uggoth/EastDevonPirates2024/STL/ZyderBot 8 Front Window B.stl

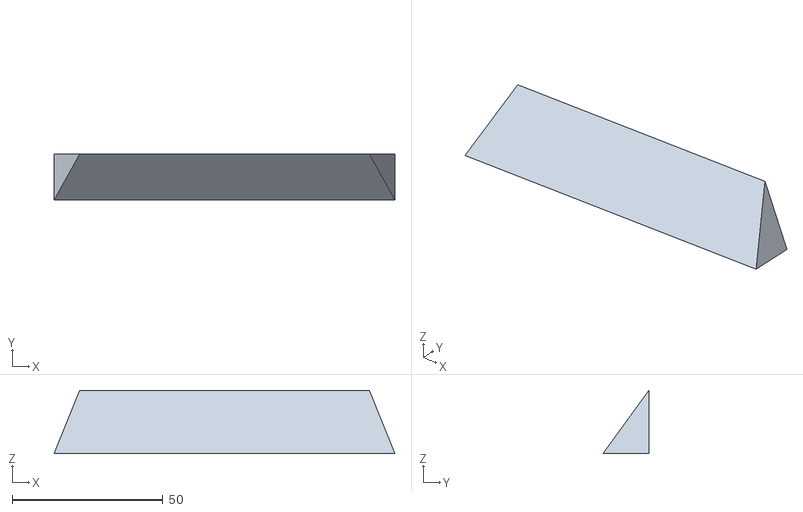
[picture p17: CAD file, 2023-10-29]
STL/ZyderBot 8 Front Window B.stl
113.0 x 15.3 x 21.0
