uggoth/EastDevonPirates2024/STL/ZyderBot 8 Chassis RTD.stl

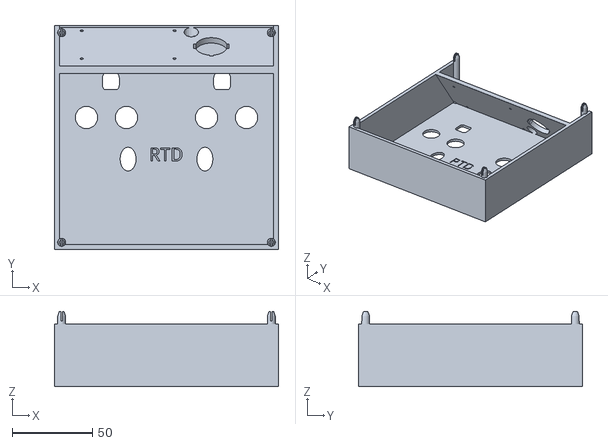
[picture p18: CAD file, 2023-10-29]
STL/ZyderBot 8 Chassis RTD.stl
140.0 x 140.0 x 47.0
