uggoth/EastDevonPirates2024/PicoCode/main_a_s_a_d_constants.py

module_name = 'main_a_s_a_d_constants.py'
print (module_name, 'starting')

PICO_NAME = 'PICOA'
BLUE_BUTTON_PIN_NO = 5
DIP_1_PIN_NO = 13
DIP_5_PIN_NO = 17
DIP_6_PIN_NO = 16
UART_TX_PIN_NO = 0
UART_RX_PIN_NO = 1
UART_NO = 0
UART_BAUD_RATE = 100000
LF_SPEED_PIN_NO = 2
LF_PULSE_PIN_NO = 3
LF_DIRECTION_PIN_NO = 4
RF_SPEED_PIN_NO = 6
RF_PULSE_PIN_NO = 7
RF_DIRECTION_PIN_NO = 8
LB_SPEED_PIN_NO = 10
LB_PULSE_PIN_NO = 11
LB_DIRECTION_PIN_NO = 12
RB_SPEED_PIN_NO = 21
RB_PULSE_PIN_NO = 20
RB_DIRECTION_PIN_NO = 19
HANDSHAKE_PIN_NO = 22
