uggoth/EastDevonPirates2024/PiCode/ColObjects_Pi_V15.py

module_name = 'ColObjects_v14.py'
module_created_at = '202305011105'

import math
import time

class ColError(Exception):
    def __init__(self, message):
        super().__init__(message)

class ColObj():
    
    allocated = {}
    free_code = 'FREE'
    
    def str_allocated():
        out_string = ('{:18}'.format('NAME') +
                        '{:18}'.format('OBJECT') + '\n')
        for name in sorted(ColObj.allocated):
            if ColObj.allocated[name] != ColObj.free_code:
                obj = ColObj.allocated[name]
                out_string += ('{:18}'.format(obj.name)  +
                                str(obj) + '\n')
        return out_string
    
    def __init__(self, name, description=''):
        self.name = name
        if name in ColObj.allocated:
            if ColObj.allocated[self.name] != ColObj.free_code:
                raise ColError(name + ' already allocated')
        ColObj.allocated[self.name] = self
        self.description = description
        
    def __str__(self):
        return self.name
    
    def close(self):
        ColObj.allocated[self.name] = ColObj.free_code

class Servo(ColObj):
    def __init__(self, name, description='Generic Servo'):
        super().__init__(name, description)
    def move_to(self, in_pos, speed):
        pos = int(in_pos)
        if pos < -100:
            raise ColError('pos must be between -100 and +100')
        if pos > 100:
            raise ColError('pos must be between -100 and +100')
        if speed < 1:
            raise ColError('speed must be between 1 and 100')
        if speed > 100:
            raise ColError('speed must be between 1 and 100')
    def close(self):
        super().close()

class Switch(ColObj):
    def __init__(self, name):
        super().__init__(name)
    def get(self):
        print ('MUST OVERRIDE')
    def close(self):
        super().close()

class Interpolator(ColObj):
    def __init__(self, name, keys, values): # arrays of matching pairs
                                            # keys ascending integers
                                            # values any floats
        super().__init__(name)
        self.keys = keys
        self.values = values
    def interpolate(self, in_key):  #  input is integer
        if in_key is None:
            return None
        below_ok = False
        above_ok = False
        for i in range(len(self.keys)):
            if in_key == self.keys[i]:
                return self.values[i]
            if in_key > self.keys[i]:
                below_key = self.keys[i]
                below_value = self.values[i]
                below_ok = True
            if in_key < self.keys[i]:
                above_key = self.keys[i]
                above_value = self.values[i]
                above_ok = True
                break
        if above_ok and below_ok:
            out_value = below_value + (((in_key - below_key) / (above_key - below_key)) * (above_value - below_value))
            return out_value
        else:
            return None


class Motor(ColObj):
    def __init__(self, name):
        super().__init__(name)
    def clk(self, speed):
        raise ColError('**** Must be overriden')
    def anti(self, speed):
        raise ColError('**** Must be overriden')
    def stop(self):
        raise ColError('**** Must be overriden')
    def close(self):
        super().close()

class Side(ColObj):
    def __init__(self, name, which_side, my_motors):
        super().__init__(name)
        self.which_side = which_side
        self.my_motors = my_motors
    def __str__(self):
        outstring = ''
        outstring += self.name + '  '
        for motor in self.my_motors:
            outstring += motor.name + '  '
    def fwd(self, speed):
        for motor in self.my_motors:
            if self.which_side == 'L':
                motor.anti(speed)
            else:
                motor.clk(speed)
    def rev(self, speed):
        for motor in self.my_motors:
            if self.which_side == 'L':
                motor.clk(speed)
            else:
                motor.anti(speed)
    def drive(self, speed):
        if speed < 0:
            self.rev(-speed)
        else:
            self.fwd(speed)
    def stop(self):
        for motor in self.my_motors:
            motor.stop()
    def close(self):
        for motor in self.my_motors:
            motor.close()
        super().close()

class DriveTrain(ColObj):
    def __init__(self, name, left_side, right_side):
        super().__init__(name)
        self.left_side = left_side
        self.right_side = right_side
        self.millimetre_factor = 30
        self.degree_factor = 30
        self.speed_exponent = 0.5          
        keys = [-101, -50, -2, 2, 50, 101]
        values = [1.0, 1.0, 1.0, 1.0, 0.0, -1.0]
        self.left_side_interpolator = Interpolator(name+'_remls',keys, values)
        values = [-1.0, 0.0, 1.0, 1.0, 1.0, 1.0]
        self.right_side_interpolator = Interpolator(name+'_remrs',keys, values)
    def calculate_speeds_car(self, throttle_value, steering_value):
        if ((throttle_value is None) or (steering_value is None)):
            return 0,0
        left_factor = self.left_side_interpolator.interpolate(steering_value)
        right_factor = self.right_side_interpolator.interpolate(steering_value)
        left_speed = int(throttle_value * left_factor)
        right_speed = int(throttle_value * right_factor)
        return left_speed, right_speed
    def drive(self, throttle_value, steering_value):
        left_speed, right_speed = self.calculate_speeds_car(throttle_value, steering_value)
        self.left_side.drive(left_speed)
        self.right_side.drive(right_speed)
    def fwd(self, speed=50, millimetres=50):
        self.left_side.fwd(speed)
        self.right_side.fwd(speed)
        if millimetres > 0:
            ms = self.convert_millimetres_to_milliseconds(millimetres, speed)
            time.sleep_ms(ms)
            self.stop()
            return ms
        return 0
    def rev(self, speed=50, millimetres=50):
        self.left_side.rev(speed)
        self.right_side.rev(speed)
        if millimetres > 0:
            ms = self.convert_millimetres_to_milliseconds(millimetres, speed)
            time.sleep_ms(ms)
            self.stop()
            return ms
        return 0
    def spl(self, speed=90, degrees=90):
        self.left_side.rev(speed)
        self.right_side.fwd(speed)
        if degrees > 0:
            ms = self.convert_degrees_to_milliseconds(degrees, speed)
            time.sleep_ms(ms)
            self.stop()
            return ms
        return 0
    def spr(self, speed=90, degrees=90):
        self.left_side.fwd(speed)
        self.right_side.rev(speed)
        if degrees > 0:
            ms = self.convert_degrees_to_milliseconds(degrees, speed)
            time.sleep_ms(ms)
            self.stop()
            return ms
        return 0
    def stop(self):
        self.left_side.stop()
        self.right_side.stop()
    def convert_millimetres_to_milliseconds(self, millimetres, speed):
        milliseconds = int (float(millimetres * self.millimetre_factor) / math.pow(speed, self.speed_exponent))
        return milliseconds
    def convert_degrees_to_milliseconds(self, millimetres, speed):
        degrees = int (float(millimetres * self.degree_factor) / math.pow(speed, self.speed_exponent))
        return degrees

class DriveTrainWithHeadlights(DriveTrain):
    def __init__(self, name, left_side, right_side, left_headlight, right_headlight):
        super().__init__(name, left_side, right_side)
        self.left_headlight = left_headlight
        self.right_headlight = right_headlight
    def fwd(self, speed=50, millimetres=50):
        self.left_headlight.on()
        self.right_headlight.on()
        super().fwd(speed, millimetres)
    def rev(self, speed=50, millimetres=50):
        self.left_headlight.red()
        self.right_headlight.red()
        super().rev(speed, millimetres)
    def spl(self, speed=90, degrees=90):
        self.left_headlight.purple()
        self.right_headlight.off()
        super().spl(speed, degrees)
    def spr(self, speed=90, degrees=90):
        self.left_headlight.off()
        self.right_headlight.purple()
        super().spr(speed, degrees)
    def stop(self):
        self.left_headlight.off()
        self.right_headlight.off()
        super().stop()

class DriveTrainPlus(DriveTrainWithHeadlights):
    def __init__(self, name, left_side, right_side, left_headlight, right_headlight,
                 front_left_ir, front_right_ir, rear_left_ir, rear_right_ir):
        super().__init__(name, left_side, right_side, left_headlight, right_headlight)
        self.front_left_ir = front_left_ir
        self.front_right_ir = front_right_ir
        self.rear_left_ir = rear_left_ir
        self.rear_right_ir = rear_right_ir
    def drive_for(self, throttle_value, steering_value, milliseconds):
        self.drive(throttle_value, steering_value)
        time.sleep_ms(milliseconds)
        self.stop()
    def drive_while(self, throttle_value, steering_value, obj_list):
        self.drive(throttle_value, steering_value)
        loop_count = 0
        loop_duration = 5
        all_ok = True
        while all_ok:
            for i in range(len(obj_list)):
                obj = obj_list[i][0]
                state = obj_list[i][1]
                current = obj.get()
                if current != state:
                    all_ok = False
            time.sleep_ms(loop_duration)
            loop_count += 1
            current = obj.get()
        self.stop()
        return loop_count * loop_duration

class DriveCalc():
    
    def __init__(self, min_throttle, max_throttle, min_steering, max_steering):
        self.min_throttle = min_throttle
        self.max_throttle = max_throttle
        self.min_steering = min_steering
        self.max_steering = max_steering

    def constrain(self, n, lowest, highest):
        if n > highest:
            a = highest
        elif n < lowest:
            a = lowest
        else:
            a = n
        return a
        
    def get_drive_parms(self, mode, throttle, steering):
        #  returns left side speed, right side speed
        if mode == 'TANK':
            left = self.constrain (throttle, self.min_throttle, self.max_throttle)
            right = self.constrain (steering, self.min_steering, self.max_steering)
            return int(left), int(right)
        if mode == 'MIX':
            left = self.constrain (throttle + steering, self.min_throttle, self.max_throttle)
            right = self.constrain (throttle - steering, self.min_throttle, self.max_throttle)
            return int(left), int(right)


class RGBLED(ColObj):
    def __init__(self, name, red_led, green_led, blue_led):
        response = super().__init__(name)
        self.red_led = red_led
        self.green_led = green_led
        self.blue_led = blue_led
        
    def on(self):
        self.red_led.on()
        self.green_led.on()
        self.blue_led.on()

    def red(self):
        self.red_led.on()
        self.green_led.off()
        self.blue_led.off()

    def green(self):
        self.red_led.off()
        self.green_led.on()
        self.red_led.off()

    def blue(self):
        self.red_led.off()
        self.green_led.off()
        self.blue_led.on()

    def purple(self):
        self.red_led.on()
        self.green_led.off()
        self.blue_led.on()

    def orange(self):
        self.red_led.on()
        self.green_led.on()
        self.blue_led.off()

    def off(self):
        self.red_led.off()
        self.green_led.off()
        self.blue_led.off()
        
    def close(self):
        self.off()
        self.red_led.close()
        self.green_led.close()
        self.blue_led.close()

if __name__ == "__main__":
    print (module_name,'was created at',module_created_at)
    #d1 = PIO('Fred',1)
    #d2 = PIO('Bill',1)
    #d3 = PIO('George',0)
    #print (PIO.str_allocated())
    #PIO.deallocate(4)
    #print (PIO.str_allocated())
