uggoth/EastDevonPirates2024/PiCode/posing_setup_small_v25.py

module_name = 'posing_setup_small_v25.py'

print (module_name, 'starting')

import tkinter as tk
import AX12_Servo_V01 as AX12_Servo
Connection = AX12_Servo.Connection

class ServoSlider:
    def __init__(self, master, x_origin, y_origin, servo):
        self.master = master
        self.servo = servo
        self.my_name = self.servo.name
        self.my_min = -100
        self.my_max = 100
        self.my_var = tk.IntVar()
        self.my_slider = tk.Scale(master, command=self.slider_moved,
                                    from_=self.my_min,
                                    to=self.my_max,
                                    length=650, sliderlength=20, variable=self.my_var,
                                    orient=tk.HORIZONTAL, label=self.servo.name)
        pos = servo.get_position()
        self.my_slider.set(pos)
        self.my_slider.place(x=x_origin,y=y_origin)
        self.previous = {}
        self.previous['POS'] = 0
        self.ok_colour = '#EEEEEE'
        self.bad_colour = '#FF7777'
        self.clock_label = tk.Label(master, text='<<<  ' + self.servo.clockwise_label, bg=self.ok_colour)
        self.clock_label.place(x=x_origin + 150, y=y_origin)
        self.pos_label = tk.Label(master, text='POS: '+str(self.previous['POS']), bg=self.ok_colour)
        self.pos_label.place(x=x_origin + 300, y=y_origin)
        self.anti_label = tk.Label(master, text=self.servo.anticlockwise_label + '  >>>', bg=self.ok_colour)
        self.anti_label.place(x=x_origin + 450, y=y_origin)
        self.passive = False

    def get_pos_text(self, position):
        return 'POS: ' + str(position)
        
    def move_to_position(self, position):
        self.passive = False
        self.my_slider.set(position)

    def slider_moved(self, value):
        if not self.passive:
            self.servo.move_to(value)

    def changed(self):
        pos = self.servo.get_position()
        if pos != self.previous['POS']:
            self.pos_label.configure(text=get_pos_text(pos))
            self.previous['POS'] = pos
        return pos

    def set_slider_to_position(self, position):
        self.passive = True
        self.my_slider.set(position)
        self.passive = False

    def set_slider_to_current(self):
        self.passive = True
        position = self.servo.get_position()
        self.my_slider.set(position)
        self.passive = False

    def set_label_to_position(self, position):
        self.pos_label.configure(text=self.get_pos_text(position))

    def set_label_to_current(self):
        position = self.servo.get_position()
        self.pos_label.configure(text=self.get_pos_text(position))

class Calibrator:

    def __init__(self, master, width, height, servo_list):
        self.master = master
        self.frame_width = width
        self.frame_height = height
        self.servo_list = servo_list
        self.frame = tk.Frame(master, width=self.frame_width, height=self.frame_height)
        self.frame.owning_object = self
        self.frame.pack()
        x_left = 10
        y_top = 10
        x_interval = 50
        y_interval = 70
        self.speed = 50
        self.speed_factor = 2
        self.sliders = {}
        x_now = x_left
        y_now = y_top
        for servo in self.servo_list:
            self.sliders[servo.name] = ServoSlider(self.frame, x_now, y_now, servo)
            y_now += y_interval

#       SPEED

        x_now = x_left
        y_now += y_interval
        self.speed_var = tk.IntVar()
        self.speed_slider = tk.Scale(self.frame, command=self.speed_change,
                                        from_=0,
                                        to=100,
                                        length=350, sliderlength=20, variable=self.speed_var,
                                        orient=tk.HORIZONTAL, label='SPEED')
        self.speed_slider.set(50)
        self.speed_slider.place(x=x_now,y=y_now)
        
#       INDICATORS
#        x_now += (x_interval * 8)
#        self.volts = voltage_monitor.VoltageMonitor(self.frame, x_now, y_now, 'WRIS')
#        x_now += (x_interval * 3)
#        self.down_ir = ir_monitor.IRMonitor(self.frame, x_now, y_now,'DOWN_IR')

    def get_speed(self):
        return int(self.speed_var.get()) * self.speed_factor

    def speed_change(self, slider_position):
        self.speed = self.get_speed()


def my_loop(my_calibrator):
    for servo in my_calibrator.servo_list:
        my_calibrator.sliders[servo.name].set_label_to_current()
#    my_calibrator.down_ir.set_text()
#    my_calibrator.volts.set_text()
    root.after(10, my_loop, my_calibrator)   # milliseconds

ax12_connection = Connection(port='/dev/serial/by-id/usb-FTDI_USB__-__Serial_Converter_FT4TCSBK-if00-port0', baudrate=1000000)
base_servo = AX12_Servo.AX12_Servo('Base Servo', ax12_connection, 11)
shoulder_servo = AX12_Servo.AX12_Servo('Shoulder Servo', ax12_connection, 10)

arm_servos = [base_servo, shoulder_servo]

root = tk.Tk()
root.title('Arm Calibration')
my_calibrator = Calibrator(root, 750, 990, arm_servos)
root.after(10,my_loop, my_calibrator)
root.mainloop()


for servo in arm_servos:
    servo.close()
ax12_connection.close()
