uggoth/EastDevonPirates2024/PicoCode/PicPicoR/test_01_B_IR_Sensors_v01.py

import ThisPico_R_V34 as ThisPico
import utime

module_name = 'test_01_B_IR_Sensors_v01.py'

print (module_name, "starting")

my_irs = ThisPico.TheseIRSensors()

for sensor in my_irs.ir_list:
    sensor.previous = 'UNKNOWN'

for i in range(1900):
    utime.sleep(0.01)
    for sensor in my_irs.ir_list:
        current = sensor.get()
        name = sensor.name
        if current != sensor.previous:
            sensor.previous = current
            print (name,'is now',current)

print (module_name, "finished")
