uggoth/EastDevonPirates2024/PiCode/test_15_M_wall_tracking_v13.py

module_name = 'test_15_M_wall_tracking_v13.py'
print (module_name,'starting')
print ('expects main_a_s_a_d to be running on the Pico')

from importlib.machinery import SourceFileLoader
data_module = SourceFileLoader('Colin', '/home/pi/ColinThisPi/ColinData.py').load_module()
data_object = data_module.ColinData()
data_values = data_object.params
ColObjectsVersion = data_values['ColObjects']
col_objects_name = '/home/pi/ColinPiClasses/' + ColObjectsVersion + '.py'
ColObjects = SourceFileLoader('ColObjects', col_objects_name).load_module()
ThisPiVersion = data_values['ThisPi']
ThisPi = SourceFileLoader('ThisPi', '/home/pi/ColinThisPi/' + ThisPiVersion + '.py').load_module()
CommandStream = SourceFileLoader('CommandStream', '/home/pi/ColinPiClasses/' + data_values['CommandStream'] + '.py').load_module()
from vl53l5cx.vl53l5cx import VL53L5CX
import time
import sys
import pigpio
gpio = pigpio.pi()
my_ultrasonics = ThisPi.Ultrasonics(gpio)
my_front_ultrasonic = my_ultrasonics.front_ultrasonic.instance

def get_offsets():
    front_mms = my_front_ultrasonic.read_mms()
    max_fails = 9
    for i in range(max_fails):
        time.sleep(0.02)
        if driver.check_data_ready():
            ranging_data = driver.get_ranging_data()
            st03 = ranging_data.target_status[driver.nb_target_per_zone * 3]
            st02 = ranging_data.target_status[driver.nb_target_per_zone * 2]
            st01 = ranging_data.target_status[driver.nb_target_per_zone * 1]
            st00 = ranging_data.target_status[driver.nb_target_per_zone * 0]
            if ((st03 == 5) and (st02 == 5) and (st01 == 5) and (st00 == 5)):
                mm03 = int(ranging_data.distance_mm[driver.nb_target_per_zone * 3])
                mm02 = int(ranging_data.distance_mm[driver.nb_target_per_zone * 2])
                mm01 = int(ranging_data.distance_mm[driver.nb_target_per_zone * 1])
                mm00 = int(ranging_data.distance_mm[driver.nb_target_per_zone * 0])
                return True, mm03, mm02, mm01, mm00, front_mms
    print ('**** No vl53 ranging data found within ',max_fails,'attempts ****')
    command = 'STOP'
    print (command, next_command(command))
    command = 'SRED'
    print (command, next_command(command))
    time.sleep(15)
    print ('ABANDON RUN')
    return False, 0.0, 0.0, 0.0, 0.0, 0.0
        
def check_straight():
    success, mm03, mm02, mm01, mm00, front_mms = get_offsets()
    if success:
        back = (mm03+mm02)/2
        front = (mm01+mm00)/2
        diff = back - front
        #print ('diff:{:4}  mm03:{:4}  mm02:{:4}  mm01:{:4}  mm00:{:4}  front_mms:{:4}'.format(
         #   diff, mm03, mm02, mm01, mm00, front_mms))
        return True, diff
    else:
        return False, 0

def straighten_up(attempts):
    success = False
    left_count = 0
    right_count = 0
    for i in range(attempts):
        time.sleep(0.05)
        ok, diff = check_straight()
        if ok:
            if abs(diff) < 2:
                print ('Straight', diff)
                success = True
                break
            if diff < 0:
                command = 'TRNL0020'
                print (command)
                left_count += 1
            else:
                command = 'TRNR0020'
                print (command)
                right_count += 1
            my_pico.send_command('0000', command)
        else:
            print ('No diff')
    if left_count > right_count:
        direction = 'LEFT'
    elif right_count > left_count:
        direction = 'RIGHT'
    else:
        direction = 'NONE'
    return success, direction, left_count, right_count

def next_command(command):
    global serial_no
    serial_no += 1
    serial_no_string = '{:04}'.format(serial_no)
    return my_pico.send_command(serial_no_string, command)
   
def wait_for_blue(blue_button, poll_loops):
    flash_interval = 7
    flip_flop = False
    for i in range(poll_loops):
        time.sleep(0.01)
        if gpio.read(blue_button) == 0:
            return True
        if i%flash_interval == 0:
            flip_flop = not flip_flop
            if flip_flop:
                next_command('SGRN')
            else:
                next_command('SOFF')
    return False

def _clamp(value, limits):
    lower, upper = limits
    if value is None:
        return None
    elif (upper is not None) and (value > upper):
        return upper
    elif (lower is not None) and (value < lower):
        return lower
    return value

class PID(object):
    """A simple PID controller."""

    def __init__(
        self,
        Kp=1.0,
        Ki=0.0,
        Kd=0.0,
        wall_distance_setpoint=0,
        sample_time=0.01,
        output_limits=(None, None),
        auto_mode=True,
        proportional_on_measurement=False,
        differential_on_measurement=True,
        error_map=None,
        time_fn=None,
        starting_output=0.0,
    ):
        """
        Initialize a new PID controller.

        :param Kp: The value for the proportional gain Kp
        :param Ki: The value for the integral gain Ki
        :param Kd: The value for the derivative gain Kd
        :param wall_distance_setpoint: The initial setpoint that the PID will try to achieve
        :param sample_time: The time in seconds which the controller should wait before generating
            a new output value. The PID works best when it is constantly called (eg. during a
            loop), but with a sample time set so that the time difference between each update is
            (close to) constant. If set to None, the PID will compute a new output value every time
            it is called.
        :param output_limits: The initial output limits to use, given as an iterable with 2
            elements, for example: (lower, upper). The output will never go below the lower limit
            or above the upper limit. Either of the limits can also be set to None to have no limit
            in that direction. Setting output limits also avoids integral windup, since the
            integral term will never be allowed to grow outside of the limits.
        :param auto_mode: Whether the controller should be enabled (auto mode) or not (manual mode)
        :param proportional_on_measurement: Whether the proportional term should be calculated on
            the input directly rather than on the error (which is the traditional way). Using
            proportional-on-measurement avoids overshoot for some types of systems.
        :param differential_on_measurement: Whether the differential term should be calculated on
            the input directly rather than on the error (which is the traditional way).
        :param error_map: Function to transform the error value in another constrained value.
        :param time_fn: The function to use for getting the current time, or None to use the
            default. This should be a function taking no arguments and returning a number
            representing the current time. The default is to use time.monotonic() if available,
            otherwise time.time().
        :param starting_output: The starting point for the PID's output. If you start controlling
            a system that is already at the setpoint, you can set this to your best guess at what
            output the PID should give when first calling it to avoid the PID outputting zero and
            moving the system away from the setpoint.
        """
        self.Kp, self.Ki, self.Kd = Kp, Ki, Kd
        self.wall_distance_setpoint = wall_distance_setpoint
        self.sample_time = sample_time

        self._min_output, self._max_output = None, None
        self._auto_mode = auto_mode
        self.proportional_on_measurement = proportional_on_measurement
        self.differential_on_measurement = differential_on_measurement
        self.error_map = error_map

        self._proportional = 0
        self._integral = 0
        self._derivative = 0

        self._last_time = None
        self._last_output = None
        self._last_error = None
        self._last_input = None

        if time_fn is not None:
            # Use the user supplied time function
            self.time_fn = time_fn
        else:
            import time

            try:
                # Get monotonic time to ensure that time deltas are always positive
                self.time_fn = time.monotonic
            except AttributeError:
                # time.monotonic() not available (using python < 3.3), fallback to time.time()
                self.time_fn = time.time

        self.output_limits = output_limits
        self.reset()

        # Set initial state of the controller
        self._integral = _clamp(starting_output, output_limits)

    def __call__(self, input_, dt=None):
        """
        Update the PID controller.

        Call the PID controller with *input_* and calculate and return a control output if
        sample_time seconds has passed since the last update. If no new output is calculated,
        return the previous output instead (or None if no value has been calculated yet).

        :param dt: If set, uses this value for timestep instead of real time. This can be used in
            simulations when simulation time is different from real time.
        """
        if not self.auto_mode:
            return self._last_output

        now = self.time_fn()
        if dt is None:
            dt = now - self._last_time if (now - self._last_time) else 1e-16
        elif dt <= 0:
            raise ValueError('dt has negative value {}, must be positive'.format(dt))

        if self.sample_time is not None and dt < self.sample_time and self._last_output is not None:
            # Only update every sample_time seconds
            return self._last_output

        # Compute error terms
        error = self.wall_distance_setpoint - input_
        d_input = input_ - (self._last_input if (self._last_input is not None) else input_)
        d_error = error - (self._last_error if (self._last_error is not None) else error)

        # Check if must map the error
        if self.error_map is not None:
            error = self.error_map(error)

        # Compute the proportional term
        if not self.proportional_on_measurement:
            # Regular proportional-on-error, simply set the proportional term
            self._proportional = self.Kp * error
        else:
            # Add the proportional error on measurement to error_sum
            self._proportional -= self.Kp * d_input

        # Compute integral and derivative terms
        self._integral += self.Ki * error * dt
        self._integral = _clamp(self._integral, self.output_limits)  # Avoid integral windup

        if self.differential_on_measurement:
            self._derivative = -self.Kd * d_input / dt
        else:
            self._derivative = self.Kd * d_error / dt

        # Compute final output
        output = self._proportional + self._integral + self._derivative
        output = _clamp(output, self.output_limits)

        # Keep track of state
        self._last_output = output
        self._last_input = input_
        self._last_error = error
        self._last_time = now

        return output

    def __repr__(self):
        return (
            '{self.__class__.__name__}('
            'Kp={self.Kp!r}, Ki={self.Ki!r}, Kd={self.Kd!r}, '
            'wall_distance_setpoint={self.wall_distance_setpoint!r}, sample_time={self.sample_time!r}, '
            'output_limits={self.output_limits!r}, auto_mode={self.auto_mode!r}, '
            'proportional_on_measurement={self.proportional_on_measurement!r}, '
            'differential_on_measurement={self.differential_on_measurement!r}, '
            'error_map={self.error_map!r}'
            ')'
        ).format(self=self)

    @property
    def components(self):
        """
        The P-, I- and D-terms from the last computation as separate components as a tuple. Useful
        for visualizing what the controller is doing or when tuning hard-to-tune systems.
        """
        return self._proportional, self._integral, self._derivative

    @property
    def tunings(self):
        """The tunings used by the controller as a tuple: (Kp, Ki, Kd)."""
        return self.Kp, self.Ki, self.Kd

    @tunings.setter
    def tunings(self, tunings):
        """Set the PID tunings."""
        self.Kp, self.Ki, self.Kd = tunings

    @property
    def auto_mode(self):
        """Whether the controller is currently enabled (in auto mode) or not."""
        return self._auto_mode

    @auto_mode.setter
    def auto_mode(self, enabled):
        """Enable or disable the PID controller."""
        self.set_auto_mode(enabled)

    def set_auto_mode(self, enabled, last_output=None):
        """
        Enable or disable the PID controller, optionally setting the last output value.

        This is useful if some system has been manually controlled and if the PID should take over.
        In that case, disable the PID by setting auto mode to False and later when the PID should
        be turned back on, pass the last output variable (the control variable) and it will be set
        as the starting I-term when the PID is set to auto mode.

        :param enabled: Whether auto mode should be enabled, True or False
        :param last_output: The last output, or the control variable, that the PID should start
            from when going from manual mode to auto mode. Has no effect if the PID is already in
            auto mode.
        """
        if enabled and not self._auto_mode:
            # Switching from manual mode to auto, reset
            self.reset()

            self._integral = last_output if (last_output is not None) else 0
            self._integral = _clamp(self._integral, self.output_limits)

        self._auto_mode = enabled

    @property
    def output_limits(self):
        """
        The current output limits as a 2-tuple: (lower, upper).

        See also the *output_limits* parameter in :meth:`PID.__init__`.
        """
        return self._min_output, self._max_output

    @output_limits.setter
    def output_limits(self, limits):
        """Set the output limits."""
        if limits is None:
            self._min_output, self._max_output = None, None
            return

        min_output, max_output = limits

        if (None not in limits) and (max_output < min_output):
            raise ValueError('lower limit must be less than upper limit')

        self._min_output = min_output
        self._max_output = max_output

        self._integral = _clamp(self._integral, self.output_limits)
        self._last_output = _clamp(self._last_output, self.output_limits)

    def reset(self):
        """
        Reset the PID controller internals.

        This sets each term to 0 as well as clearing the integral, the last output and the last
        input (derivative calculation).
        """
        self._proportional = 0
        self._integral = 0
        self._derivative = 0

        self._integral = _clamp(self._integral, self.output_limits)

        self._last_time = self.time_fn()
        self._last_output = None
        self._last_input = None

serial_no = 1

handshake = CommandStream.Handshake('picoa hs', 4, gpio)
pico_id = 'PICOA'
my_pico = CommandStream.Pico(pico_id, gpio, handshake)
if not my_pico.valid:
    print ('*** NO PICO')
    sys.exit(1)
next_command('STOP')
pwren = 17
gpio.set_mode(pwren, pigpio.OUTPUT)
gpio.write(pwren,1)
driver = VL53L5CX()
alive = driver.is_alive()
if not alive:
    raise IOError("VL53L5CX Device is not alive")
print("Initialising...")
t = time.time()
driver.init()
driver.set_resolution(4*4)
max_readings_per_second = 50
readings_per_second = 20
if readings_per_second > max_readings_per_second:
    print ('readings_per_second > max_readings_per_second')
    sys.exit(1)
driver.set_ranging_frequency_hz(readings_per_second)
driver.start_ranging()
print(f"Initialised ({time.time() - t:.1f}s)")
print ('Now waiting for blue button')
blue_button = 16
gpio.set_mode(blue_button, pigpio.INPUT)
gpio.set_pull_up_down(blue_button, pigpio.PUD_UP)

max_not_ready = 100
max_bad_status = 100
no_zones = 16
legs = ['TRNR','TRNR','TRNL','TRNL','TRNR','STOP']
leg = 0
not_ready = 0
bad_status = 0
steering = 0
delay = 0

previous_offset = 0
previous_angle = 'ANGLE_OK'
stopping = False
success = False

class PID_B():
    def __init__(self, p, i, d, wall_distance_setpoint, low, high):
        self.name = 'simple PID'
        self.wall_distance_setpoint = wall_distance_setpoint
        self.simple_pid = PID(p, i, d, self.wall_distance_setpoint,
                              output_limits=(low,high))
    def __call__(self, new_reading):
        self.new_control = self.simple_pid(new_reading)
        return int(self.new_control)

parm_set = 2
if parm_set == 1:
    print ('1 Using Parameter Set', parm_set)
    p = 1.0
    i = 0.2
    d = 0.2
    low = -20
    high = 20
    base_throttle = 45
    front = 220
    interval = 300  #  milliseconds
    wall_distance_setpoint = 200
    wall_distance_factor = 0.1
    straightness_factor = 0.1
    obstacle_distance_factor = 0.1
elif parm_set == 2:
    print ('2 Using Parameter Set', parm_set)
    p = 1.0
    i = 0.0
    d = 0.5
    low = -40
    high = 40
    base_throttle = 35
    front = 220
    interval = 100  #  milliseconds
    wall_distance_setpoint = 200
    wall_lost = 400
    straightness_setpoint = 20
    obstacle_distance_setpoint = 300
    wall_distance_factor = 1.1
    straightness_factor = 1.1
    obstacle_distance_factor = 0.5

def calc_throttle_factor(mm00, mm01, front_mms,
                  wall_distance_factor, straightness_factor, obstacle_distance_factor,
                  wall_distance_setpoint, straightness_setpoint, obstacle_distance_setpoint):  
    throttle_factor = 1.0
    near = wall_distance_setpoint * 0.8
    far = wall_distance_setpoint * 1.3
    if ((mm00 > near) and (mm00 < far)):
        throttle_factor = throttle_factor * wall_distance_factor
    diff = abs(mm00 - mm01)
    if diff < straightness_setpoint:
        throttle_factor = throttle_factor * straightness_factor
    if front_mms < obstacle_distance_setpoint:
        throttle_factor = throttle_factor * obstacle_distance_factor
    #print ('throttle factor {:}'.format(throttle_factor))
    return throttle_factor
    
my_pid = PID_B(p, i, d, wall_distance_setpoint, low, high)

check_loops = 150
check_interval = interval / 1000.0
print ('Check Interval Is ',check_interval)
while True:
    if wait_for_blue(blue_button, 500000):
        print ('Blue button pressed. Starting ...')
    else:
        print ('Blue button not pressed. Start again')
        continue
    next_command('SGRN')
    time.sleep(2)
    next_command('SBLU')
    steering = 0
    throttle = base_throttle
    delay = 0
    command = 'DRIV{:04}{:04}{:04}'.format(steering, base_throttle, delay)
    print (command, next_command(command))
    time.sleep(1)

    for i in range(check_loops):
        time.sleep(check_interval)
        if gpio.read(blue_button) == 0:
            command = 'SRED'
            print (command, next_command(command))
            time.sleep(2)
            command = 'SGRN'
            print (command, next_command(command))
            break
        if stopping:
            print ('STOPPING BECAUSE OF HIT FRONT ETC.')
            break
        success, mm03, mm02, mm01, mm00, front_mms = get_offsets()
        if not success:
            break
        print ('front_mms', front_mms)
        if front_mms < obstacle_distance_setpoint:
            print ('Hit Front at',front_mms,' < ',obstacle_distance_setpoint)
            for j in range(9):
                command = 'TRNR  70'
                print ('A1', command, next_command(command))
                success, mm03, mm02, mm01, mm00, front_mms = get_offsets()
                if not success:
                    break
                if front_mms > obstacle_distance_setpoint:
                    break
            if not success:
                break
            straighten_up(5)
            continue
        if not success:
            stopping = True
            print ('**** no offsets ****')
            break
        avg_offset = mm00
        if avg_offset > wall_lost:
            print ('WALL LOST', avg_offset)
            command = 'DRIV   0  50 200'
            print ('B1', command, next_command(command))
            command = 'TRNL  50'
            print ('B2', command, next_command(command))
            for j in range(9):
                command = 'TRNL  70'
                print ('C1', command, next_command(command))
                success, mm03, mm02, mm01, mm00, front_mms = get_offsets()
                if not success:
                    break
                if mm00 < wall_lost:
                    break            
            continue
        avg_offset = mm00
        steering = my_pid(avg_offset)
        abs_steering = abs(steering)
        actual_throttle = int(base_throttle * calc_throttle_factor(mm00, mm01, front_mms,
                  wall_distance_factor, straightness_factor, obstacle_distance_factor,
                  wall_distance_setpoint, straightness_setpoint, obstacle_distance_setpoint)) 
        command = 'DRIV{:4}{:4}{:4}'.format(steering, actual_throttle, delay)
        print ('offs:{:3}, front:{:4}, steer:{:3}'.format(avg_offset, front_mms, steering), '\n',
               'D1', command, next_command(command), '\n')
    if i >= check_loops:
        print ('STOPPING BECAUSE OF LOOP LIMIT')
    command = 'STOP'
    print ('E1', command, next_command(command))
    command = 'HOFF'
    print (command, next_command(command))
    print (command, next_command(command))
    print (command, next_command(command))
    continue

time.sleep(1)
print (next_command('STOP'))
my_ultrasonics.close()
my_pico.close()
handshake.close()
print (module_name, 'finished')
