uggoth/EastDevonPirates2024/PicoCode/PicPicoR/ColinPicoTests/test_18_SBUS_H_drive_v01.py

module_name = 'test_18_SBUS_H_drive_v01.py'
description = 'testing object with headlights'
import ThisPico_A_V28 as ThisPico
ColObjects = ThisPico.ColObjects
import utime

my_sbus = ThisPico.ThisSbusReceiver()
print (my_sbus)
my_train = ThisPico.ThisDriveTrainWithHeadlights()
print (my_train)

while True:
    utime.sleep_ms(10)
    throttle_value, steering_value, switch_value = my_sbus.get()
    if switch_value < 0:
        break
    elif switch_value > 0:
        my_train.headlights_enabled = True
    else:
        my_train.headlights_enabled = False
    if throttle_value is None:
        continue
    else:
        my_train.drive(throttle_value, steering_value)

my_train.headlight.off()
my_train.stop()
my_train.close()
my_sbus.close()

print ('--- AFTER CLOSE --')
print (ColObjects.ColObj.str_allocated())
print (module_name, 'finished')
