uggoth/EastDevonPirates2024/PicoCode/PicPicoR/ColinPicoTests/test_01_D_switches_v03.py

module_name = 'test_01_D_switches_v03.py'

import ThisPico_D_v13 as ThisPico
GPIO = ThisPico.GPIO
import utime

print (module_name, 'starting')

these_switches = ThisPico.TheseSwitches()

my_switches = GPIO.Switch.switch_list

print ("List of switches:")
for switch in my_switches:
    print ('  ',switch.name)
    switch.previous = 'UNKNOWN'

for i in range(100):
    utime.sleep(0.1)
    for switch in my_switches:
        current = switch.get()
        if current != switch.previous:
            print (switch.name, current)
            switch.previous = current

print (module_name, 'finished')
