uggoth/EastDevonPirates2024/PicoCode/PicPicoR/ColinPicoTests/test_18_SBUS_E_v01.py

module_name = 'test_18_SBUS_E_v01.py'
description = 'testing object'
import ThisPico_A_V26 as ThisPico
ColObjects = ThisPico.ColObjects
import utime

my_sbus = ThisPico.ThisSbusReceiver()
print (my_sbus)

for i in range(19):
    throttle_value, steering_value, switch_value = my_sbus.get()
    if throttle_value is None:
        continue
    else:
        print (throttle_value, steering_value, switch_value)
    utime.sleep(0.5)

my_sbus.close()

print ('--- AFTER CLOSE --')
print (ColObjects.ColObj.str_allocated())
print (module_name, 'finished')
